ubipo/water-well-level/mcu/include/cellular.h

#pragma once


#define PIN_CELLULAR_PWR 3

#define AT_OK_STATUS 0
#define AT_ERROR_STATUS 1
#define ERROR_RECEIVING_AT_STATUS 2

unsigned char sendNoResponseCommand(Stream* modemStream, String command);
void setupCellularIO();
void setupCellular();
unsigned char checkIfCellularIsOn(unsigned long timeout, bool* isOn);
void powerOnCellular();
void powerOffCellular();
void rebootCellular();
